Scott1974-1/TL-D3/Images/IMG_0604.JPG

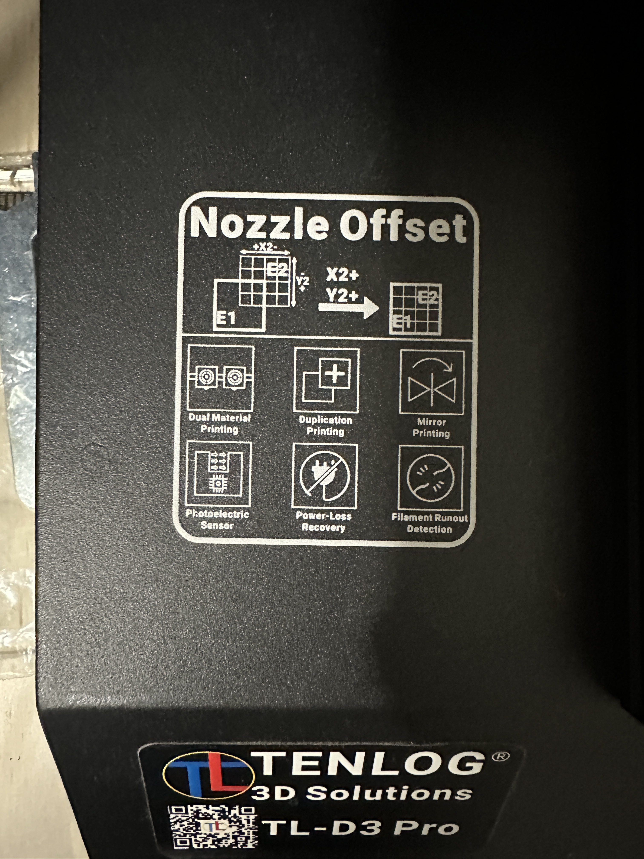
Images/IMG_0604.JPG
