Scott1974-1/TL-D3/Images/IMG_0610.JPG

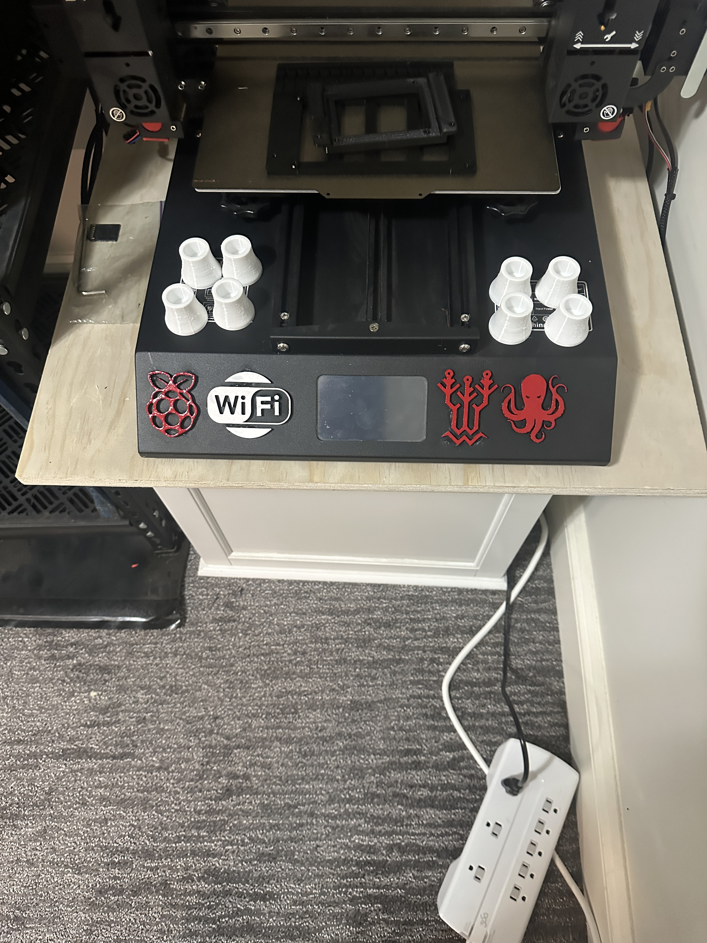
Images/IMG_0610.JPG
