Scott1974-1/TL-D3/Useful STL Files for the TL-D3 Pro /5015 Fanduct/images/cover_t1.png

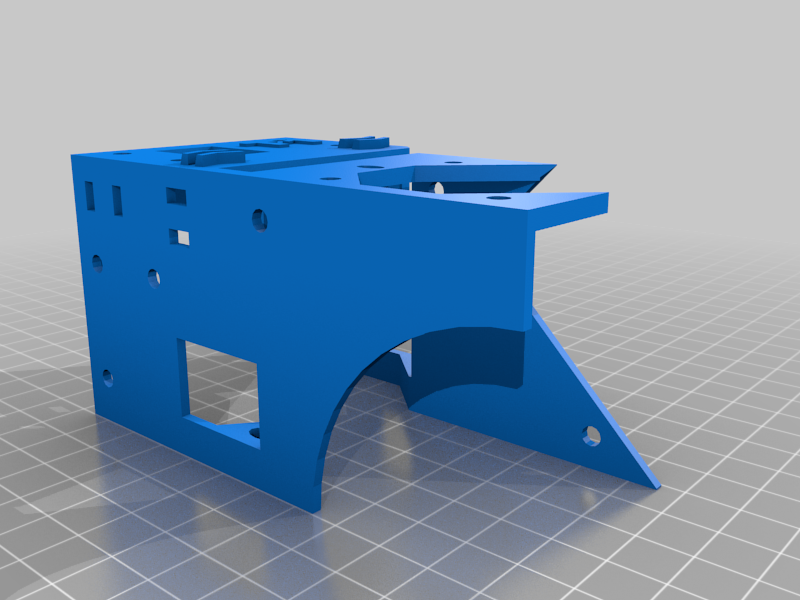
Useful STL Files for the TL-D3 Pro /5015 Fanduct/images/cover_t1.png
