Scott1974-1/TL-D3/Useful STL Files for the TL-D3 Pro /5015 Fanduct/images/DC_T1_fanduct_Text.png

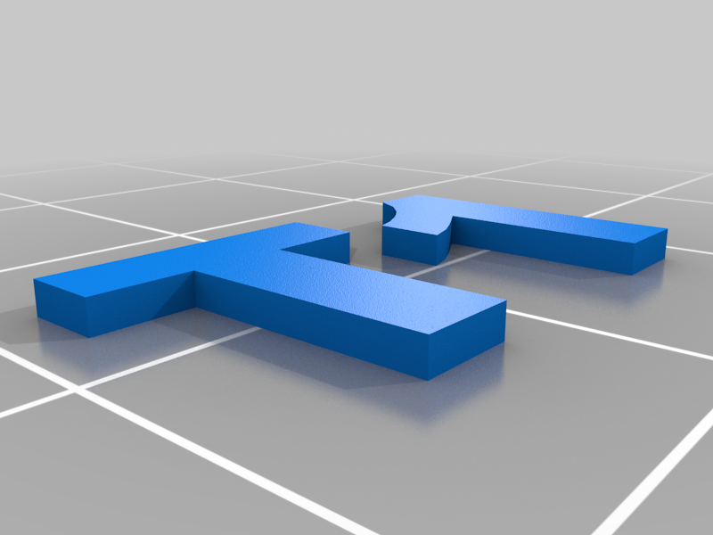
Useful STL Files for the TL-D3 Pro /5015 Fanduct/images/DC_T1_fanduct_Text.png
