Scott1974-1/TL-D3/Useful STL Files for the TL-D3 Pro /5015 Fanduct/images/foto_1.jpg

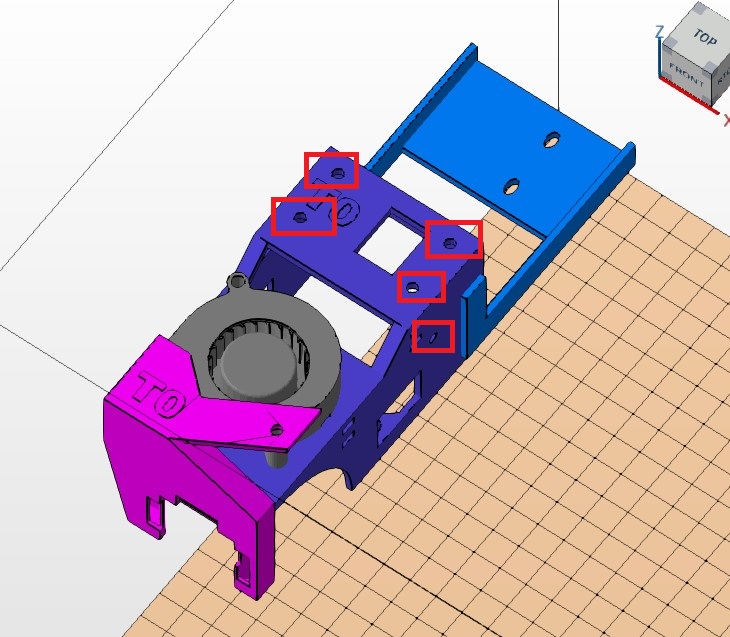
Useful STL Files for the TL-D3 Pro /5015 Fanduct/images/foto_1.jpg
