Scott1974-1/TL-D3/Useful STL Files for the TL-D3 Pro /Purge Bin w_ Modular Inserts/images/TLD3pro_Purge_Bin_3.jpg

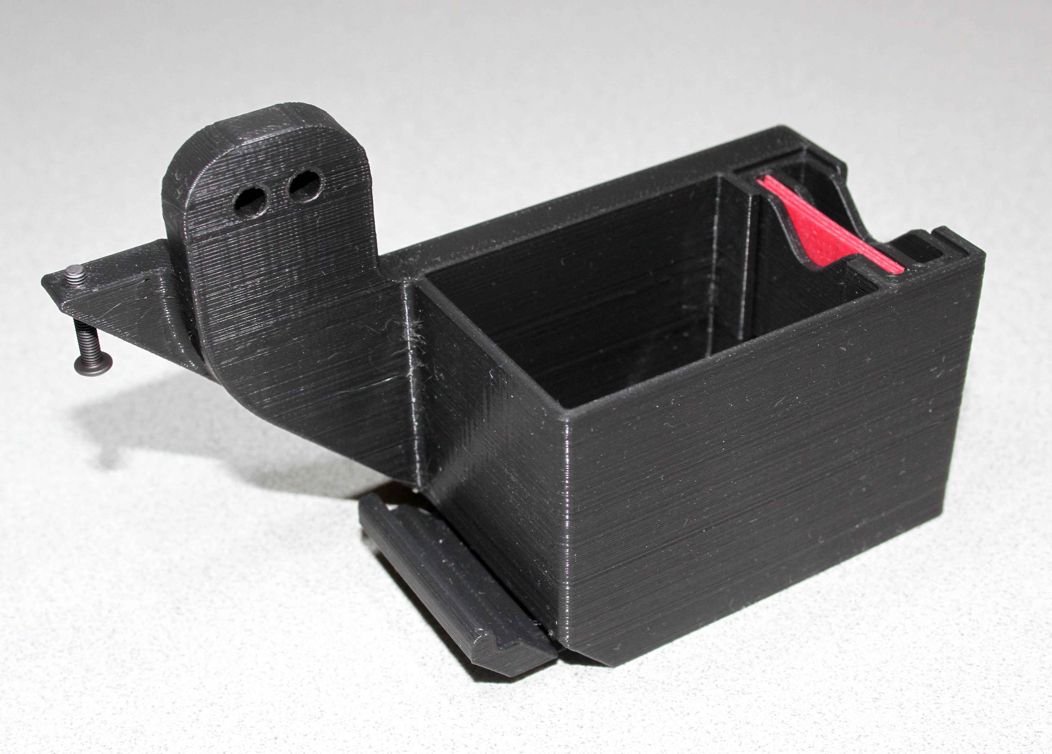
Useful STL Files for the TL-D3 Pro /Purge Bin w_ Modular Inserts/images/TLD3pro_Purge_Bin_3.jpg
