Scott1974-1/TL-D3/Useful STL Files for the TL-D3 Pro /Spool Holders/images/LH_Spool_Holder_Tenlog_TL-D3_Pro.png

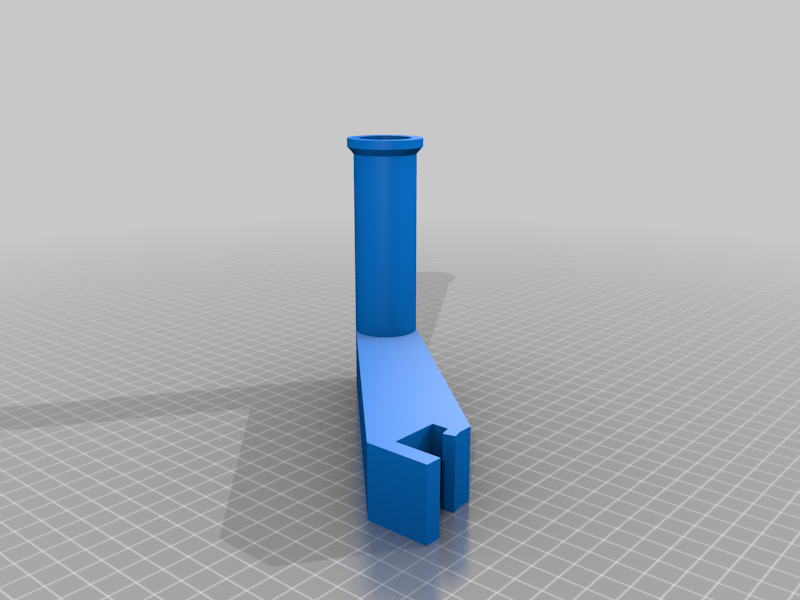
Useful STL Files for the TL-D3 Pro /Spool Holders/images/LH_Spool_Holder_Tenlog_TL-D3_Pro.png
