Scott1974-1/TL-D3/Useful STL Files for the TL-D3 Pro /Spool Holders/images/tenlog-spool-holder.jpg

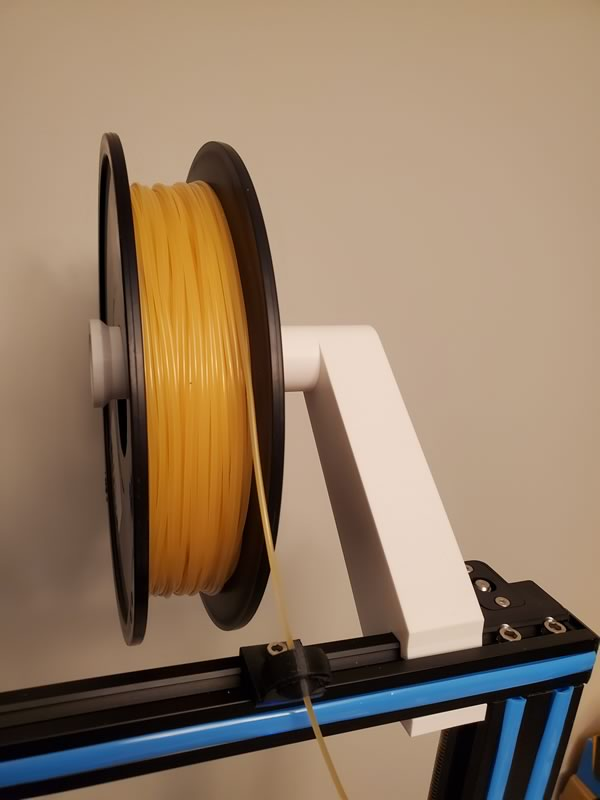
Useful STL Files for the TL-D3 Pro /Spool Holders/images/tenlog-spool-holder.jpg
