Scott1974-1/TL-D3/Useful STL Files for the TL-D3 Pro /Tenlog TL-D3 Pro TPU Foot/images/IMG_20220204_084932120.jpg

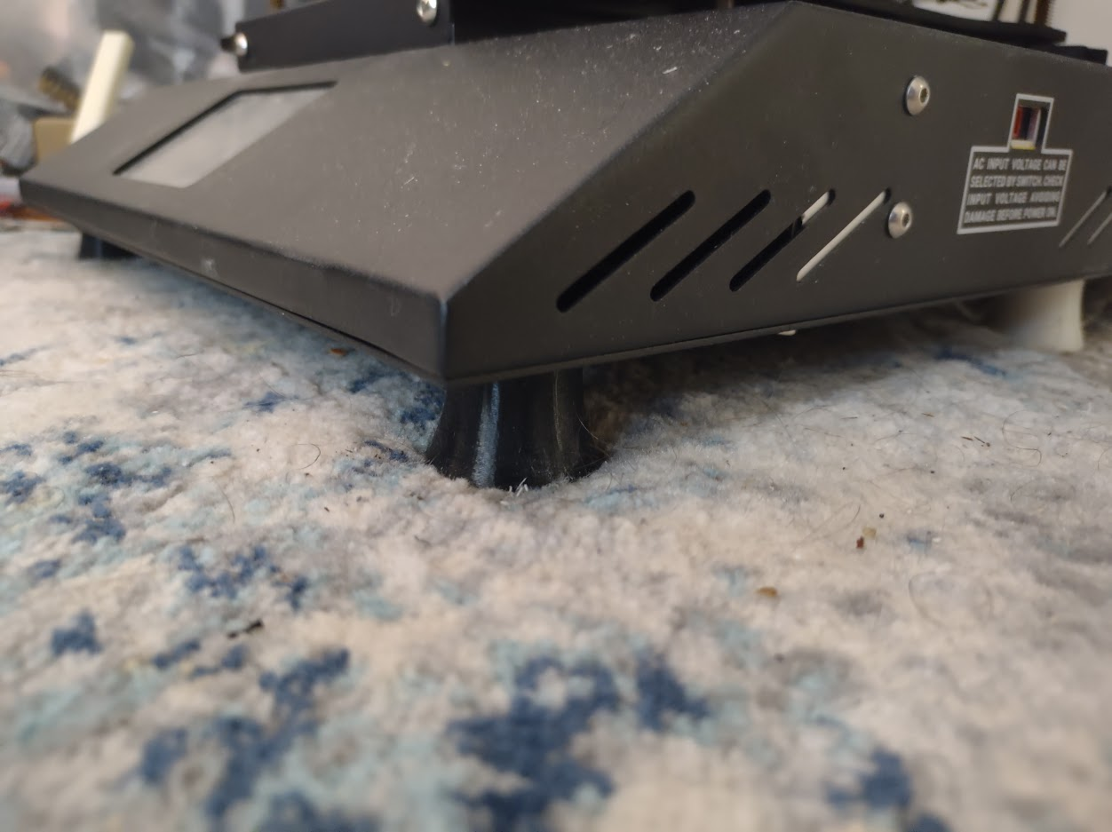
Useful STL Files for the TL-D3 Pro /Tenlog TL-D3 Pro TPU Foot/images/IMG_20220204_084932120.jpg
