Scott1974-1/TL-D3/TL-D3 Cura Profiles/meshes/TL-D4Pro.stl

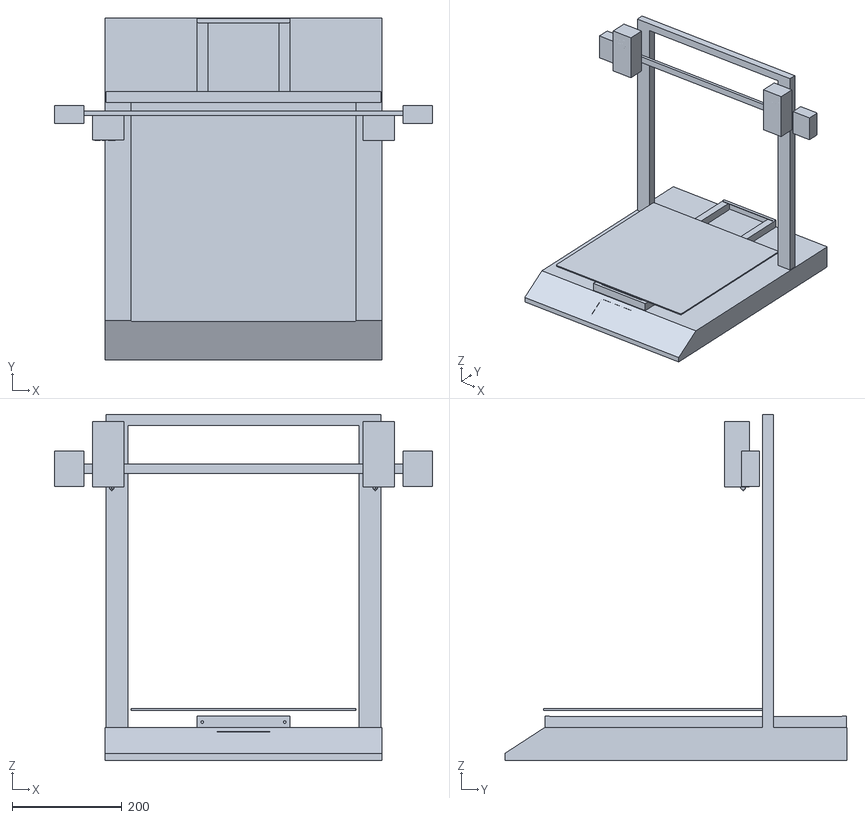
[picture p49: CAD file, 2025-01-07]
TL-D3 Cura Profiles/meshes/TL-D4Pro.stl
687.8 x 622.5 x 630.0
