Scott1974-1/TL-D3/Useful STL Files for the TL-D3 Pro /5015 Fanduct/files/DC_T0_fanduct_Text.stl

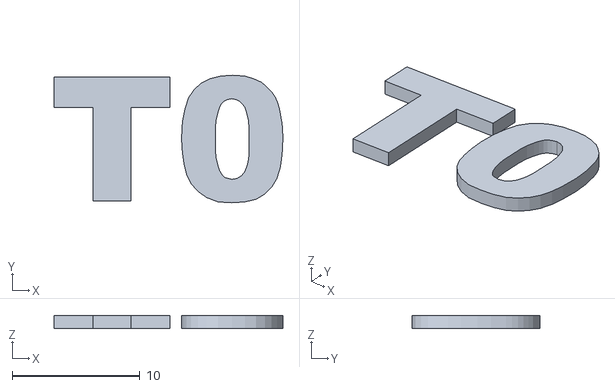
[picture p50: CAD file, 2025-01-07]
Useful STL Files for the TL-D3 Pro /5015 Fanduct/files/DC_T0_fanduct_Text.stl
18.0 x 10.0 x 1.00
