Scott1974-1/TL-D3/Useful STL Files for the TL-D3 Pro /BTT Super Case/SV03_Controller_RPI_Case.stl

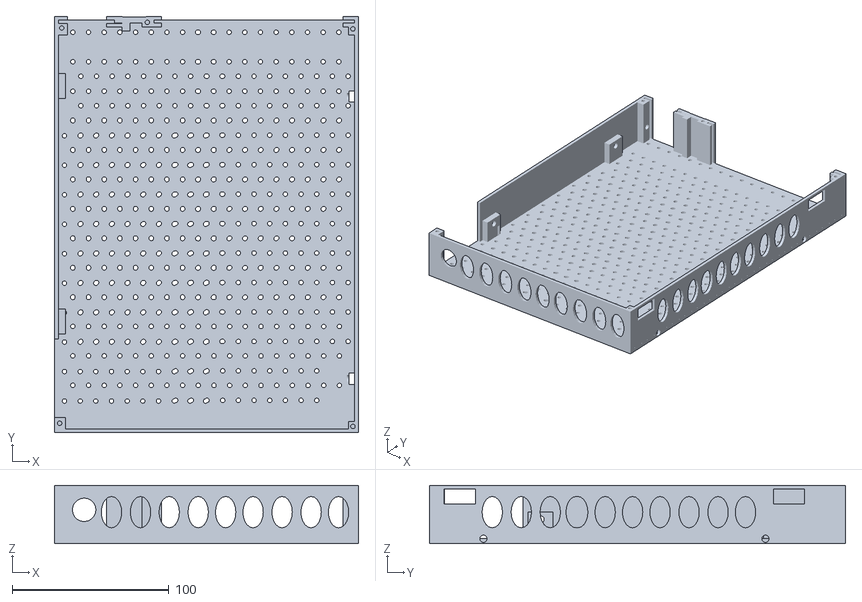
[picture p51: CAD file, 2025-01-07]
Useful STL Files for the TL-D3 Pro /BTT Super Case/SV03_Controller_RPI_Case.stl
193.9 x 265.6 x 37.0
