Scott1974-1/TL-D3/Useful STL Files for the TL-D3 Pro /Filament guide.stl

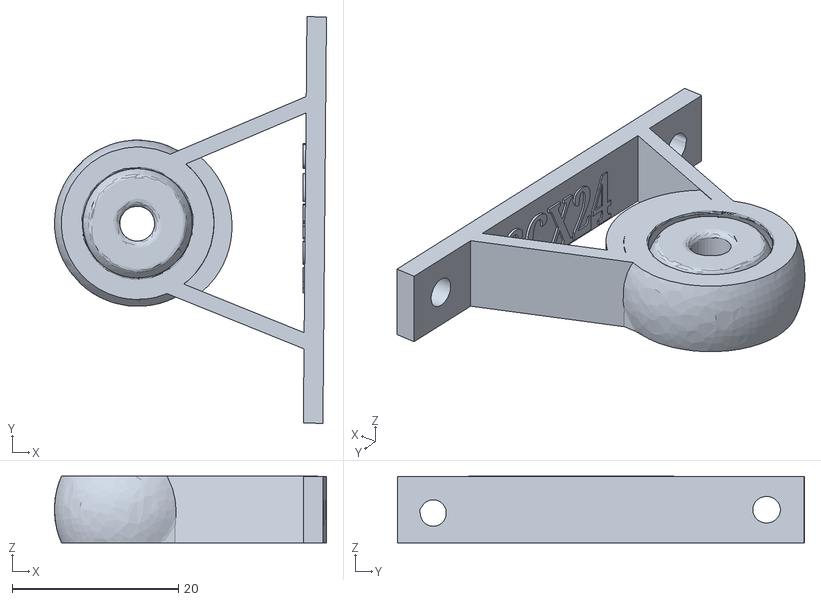
[picture p52: CAD file, 2025-01-09]
Useful STL Files for the TL-D3 Pro /Filament guide.stl
32.7 x 48.9 x 8.01
