Scott1974-1/TL-D3/Useful STL Files for the TL-D3 Pro /JST-XH Protectors /2pin/JST_Top2P-c2.stl

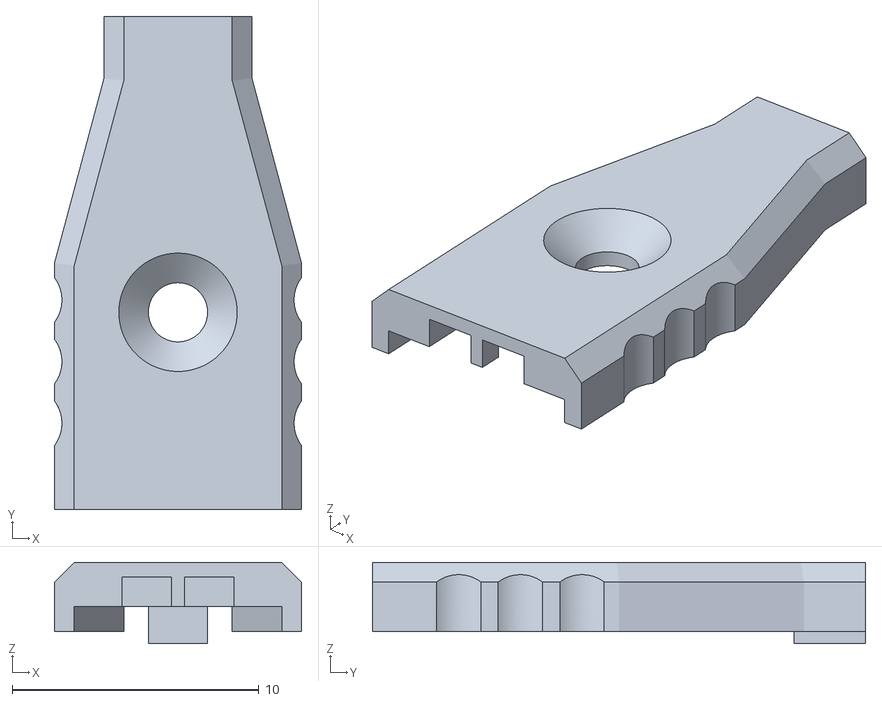
[picture p53: CAD file, 2025-01-08]
Useful STL Files for the TL-D3 Pro /JST-XH Protectors /2pin/JST_Top2P-c2.stl
10.0 x 20.0 x 3.30
