Scott1974-1/TL-D3/Useful STL Files for the TL-D3 Pro /JST-XH Protectors /3pin/JST_Top3P-c3.stl

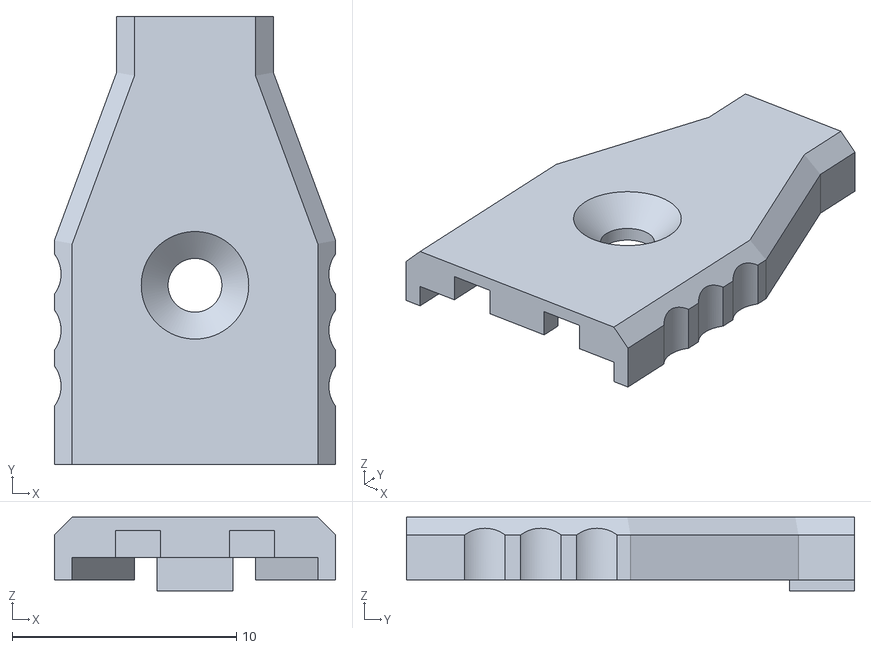
[picture p54: CAD file, 2025-01-08]
Useful STL Files for the TL-D3 Pro /JST-XH Protectors /3pin/JST_Top3P-c3.stl
12.6 x 20.0 x 3.30
