Scott1974-1/TL-D3/Useful STL Files for the TL-D3 Pro /JST-XH Protectors /4pin/JST_Top4P-c4.stl

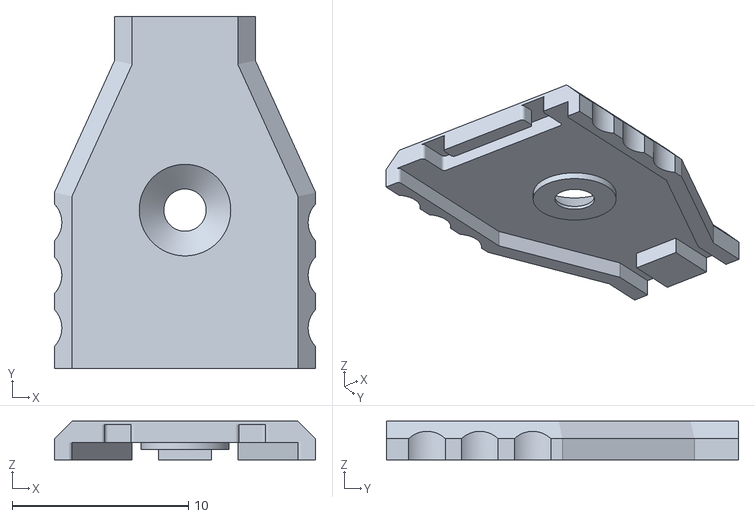
[picture p55: CAD file, 2025-01-08]
Useful STL Files for the TL-D3 Pro /JST-XH Protectors /4pin/JST_Top4P-c4.stl
14.8 x 20.0 x 2.20
