Scott1974-1/TL-D3/Useful STL Files for the TL-D3 Pro /Logos/BTT_Octopus_Logo_v3.stl

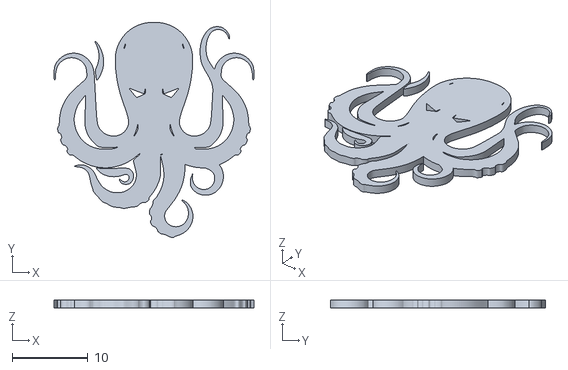
[picture p56: CAD file, 2025-01-07]
Useful STL Files for the TL-D3 Pro /Logos/BTT_Octopus_Logo_v3.stl
26.5 x 28.5 x 1.00
