Scott1974-1/TL-D3/Useful STL Files for the TL-D3 Pro /Purge Bin w_ Modular Inserts/files/TLD3pro_Purge_Bin.stl

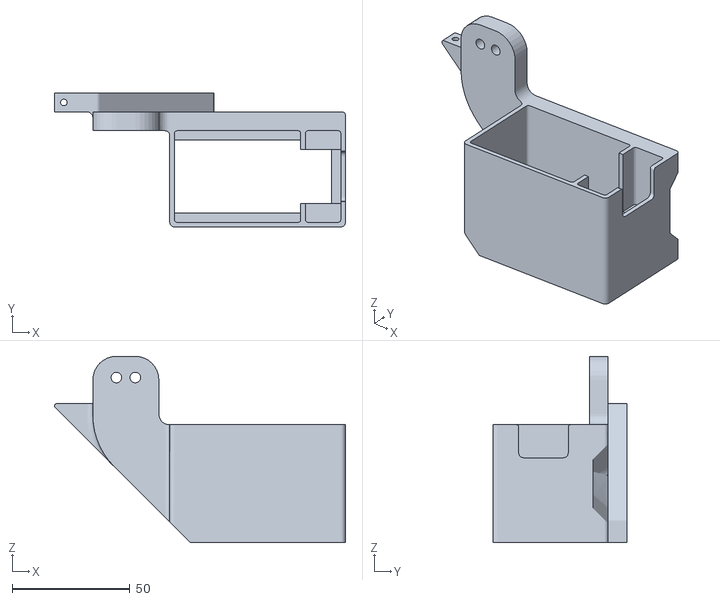
[picture p57: CAD file, 2025-01-07]
Useful STL Files for the TL-D3 Pro /Purge Bin w_ Modular Inserts/files/TLD3pro_Purge_Bin.stl
123.4 x 56.8 x 79.0
