Scott1974-1/TL-D3/Useful STL Files for the TL-D3 Pro /tenlog-tl-d3-pro-z-stabilizer/Z_bottom_right_D12_RV01.STL

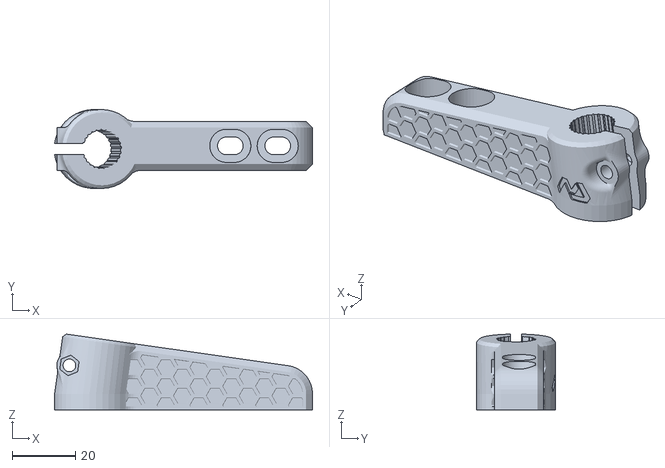
[picture p58: CAD file, 2025-01-07]
Useful STL Files for the TL-D3 Pro /tenlog-tl-d3-pro-z-stabilizer/Z_bottom_right_D12_RV01.STL
81.7 x 25.0 x 24.0
