Scott1974-1/TL-D3/Useful STL Files for the TL-D3 Pro /Testing/Bed level and nozzle offset/files/TLD_BL2.stl

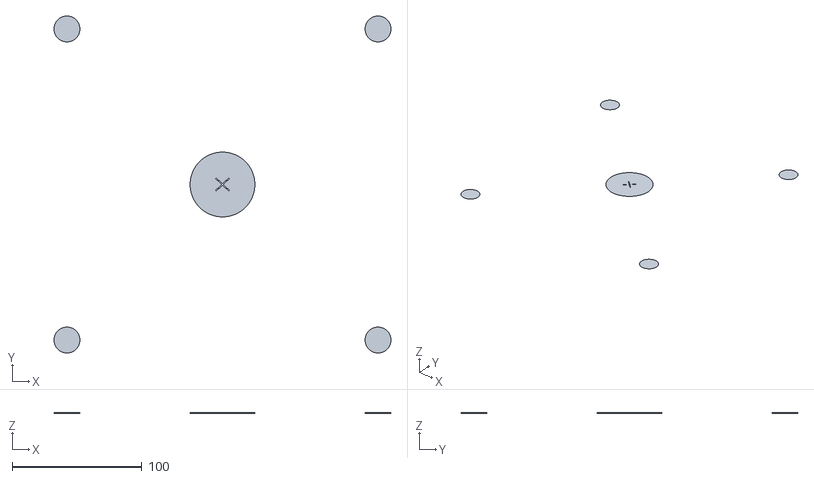
[picture p59: CAD file, 2025-01-07]
Useful STL Files for the TL-D3 Pro /Testing/Bed level and nozzle offset/files/TLD_BL2.stl
260.0 x 260.0 x 0.2
