Scott1974-1/TL-D3/TL-D3 Cura Profiles/meshes/TL-D3Pro.stl

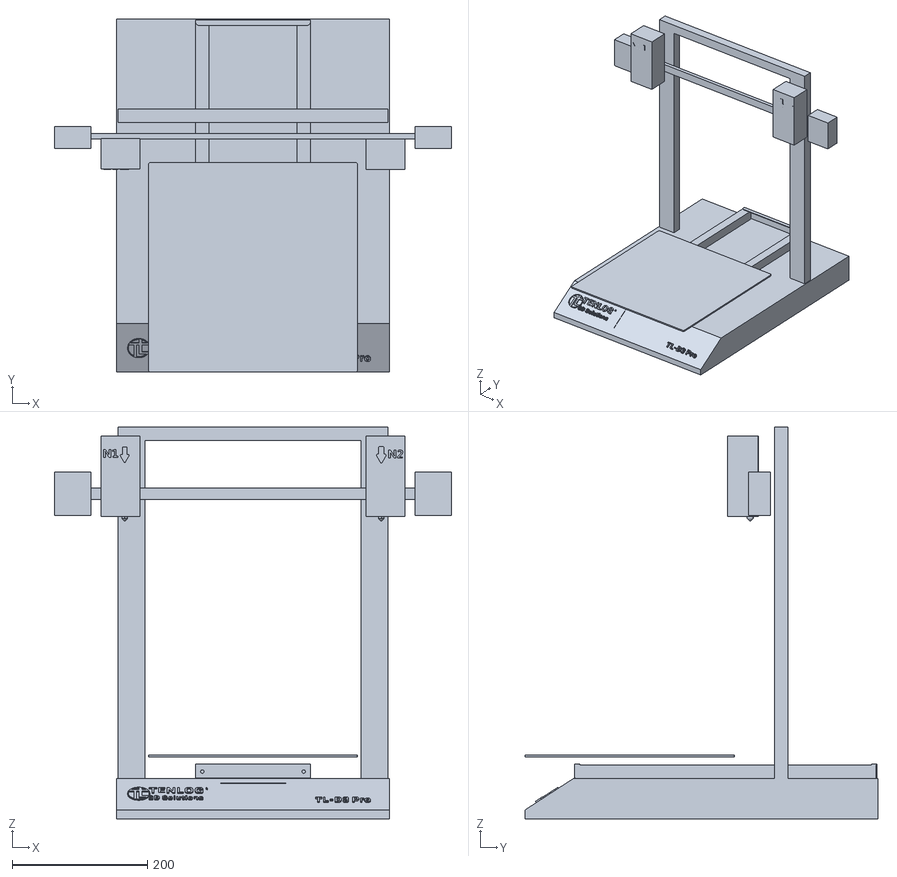
[picture p60: CAD file, 2025-01-07]
TL-D3 Cura Profiles/meshes/TL-D3Pro.stl
587.8 x 522.6 x 580.0
