Scott1974-1/TL-D3/Useful STL Files for the TL-D3 Pro /5015 Fanduct/files/DC_T1_cover_Text.stl

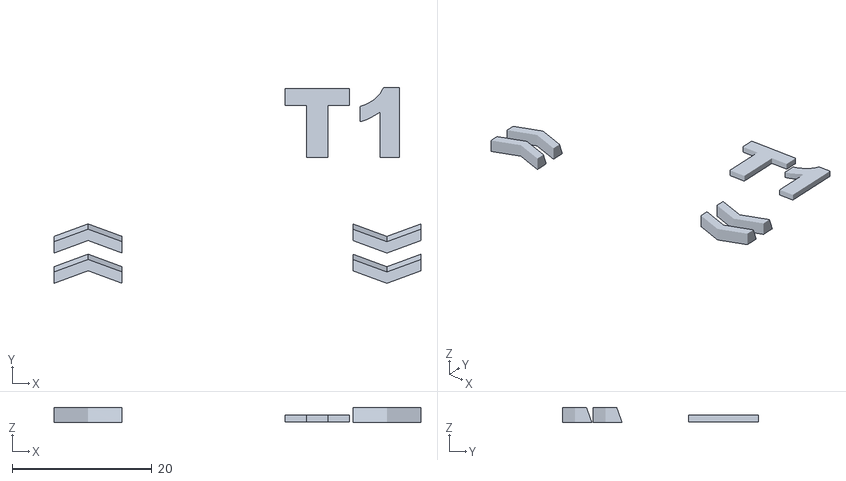
[picture p61: CAD file, 2025-01-07]
Useful STL Files for the TL-D3 Pro /5015 Fanduct/files/DC_T1_cover_Text.stl
52.5 x 28.0 x 2.10
