Scott1974-1/TL-D3/Useful STL Files for the TL-D3 Pro /Cable guide.stl

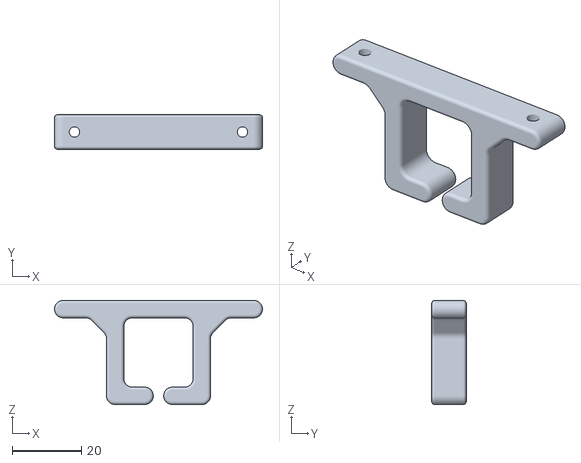
[picture p62: CAD file, 2025-01-09]
Useful STL Files for the TL-D3 Pro /Cable guide.stl
60.0 x 10.0 x 30.0
