Scott1974-1/TL-D3/Useful STL Files for the TL-D3 Pro /Purge Bin w_ Modular Inserts/files/TLD3pro_Purge_Bin_Brush_Insert.stl

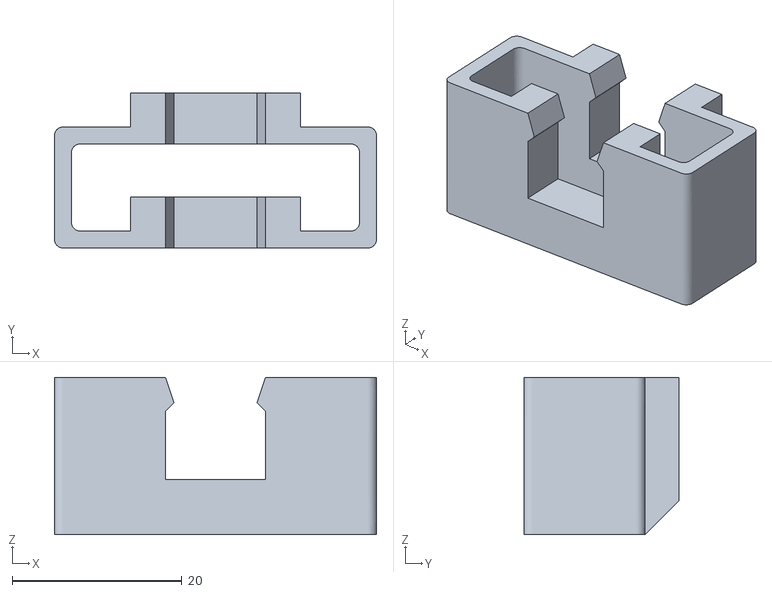
[picture p63: CAD file, 2025-01-07]
Useful STL Files for the TL-D3 Pro /Purge Bin w_ Modular Inserts/files/TLD3pro_Purge_Bin_Brush_Insert.stl
37.9 x 18.2 x 18.5
