Scott1974-1/TL-D3/TL-D3 Cura Profiles/meshes/TL-D5Pro.stl

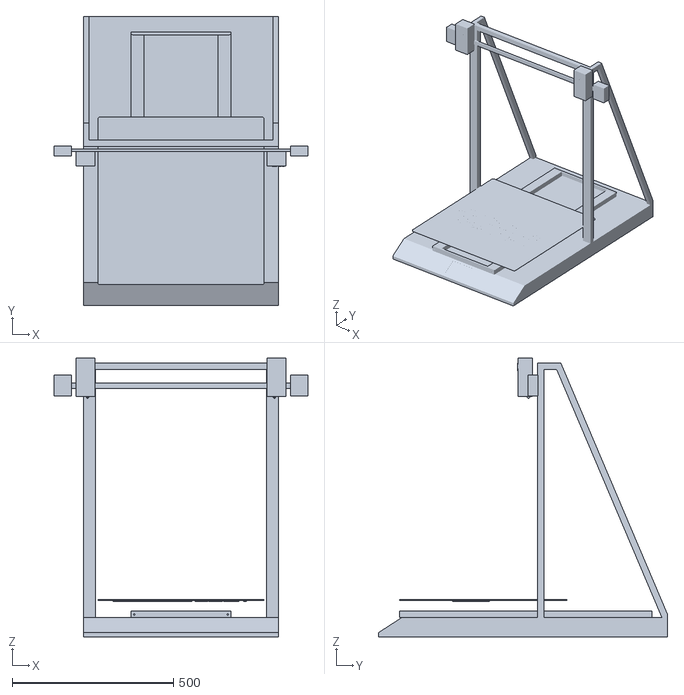
[picture p64: CAD file, 2025-01-07]
TL-D3 Cura Profiles/meshes/TL-D5Pro.stl
787.8 x 897.5 x 865.8
