Scott1974-1/TL-D3/Useful STL Files for the TL-D3 Pro /19_mm_wrench.stl

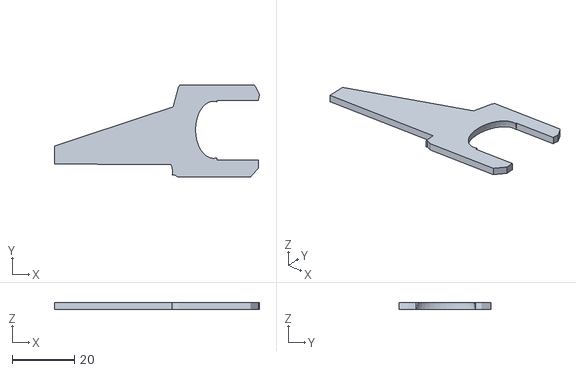
[picture p65: CAD file, 2025-01-08]
Useful STL Files for the TL-D3 Pro /19_mm_wrench.stl
65.9 x 29.7 x 2.11
