Scott1974-1/TL-D3/Useful STL Files for the TL-D3 Pro /5015 Fanduct/files/T0_cover.stl

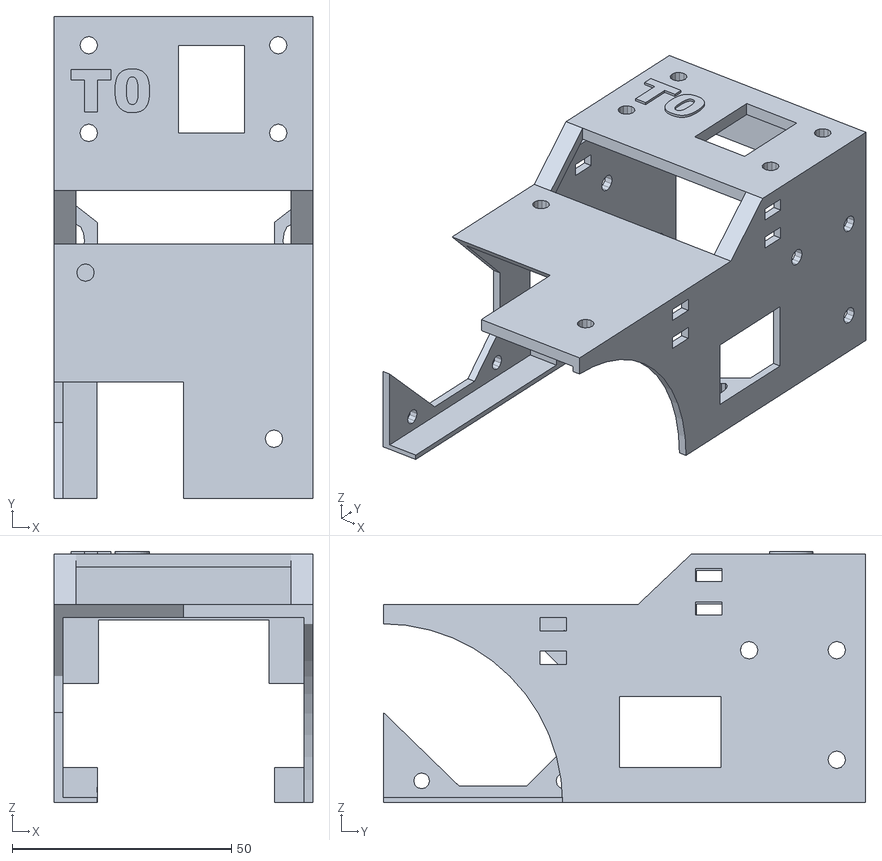
[picture p66: CAD file, 2025-01-07]
Useful STL Files for the TL-D3 Pro /5015 Fanduct/files/T0_cover.stl
59.0 x 110.0 x 57.4
