Scott1974-1/TL-D3/Useful STL Files for the TL-D3 Pro /Purge Bin w_ Modular Inserts/files/TLD3pro_Purge_Bin_Insert_Blank.stp

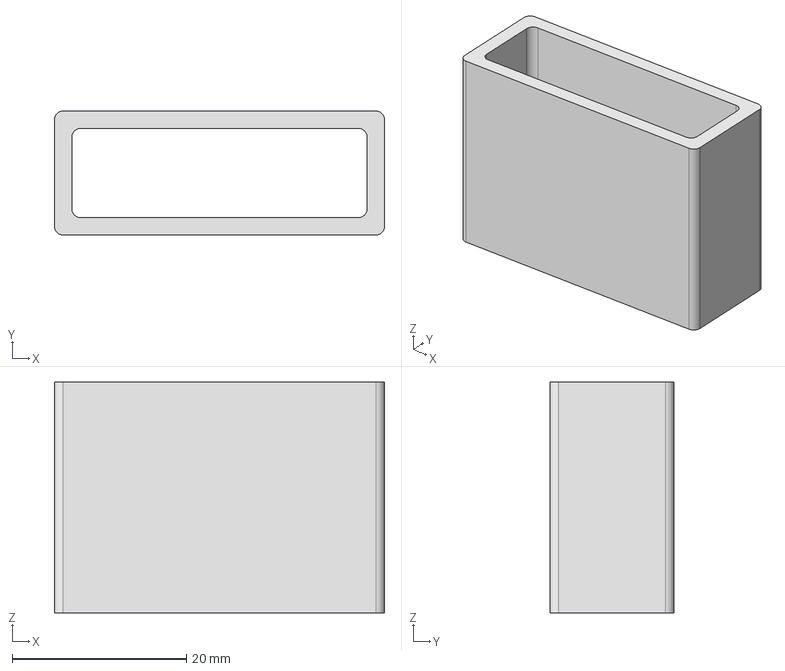
[picture p67: CAD file, 2025-01-07]
Useful STL Files for the TL-D3 Pro /Purge Bin w_ Modular Inserts/files/TLD3pro_Purge_Bin_Insert_Blank.stp
37.9 x 14.3 x 26.5 mm
