Scott1974-1/TL-D3/Useful STL Files for the TL-D3 Pro /E2_Tool_Holder.stl

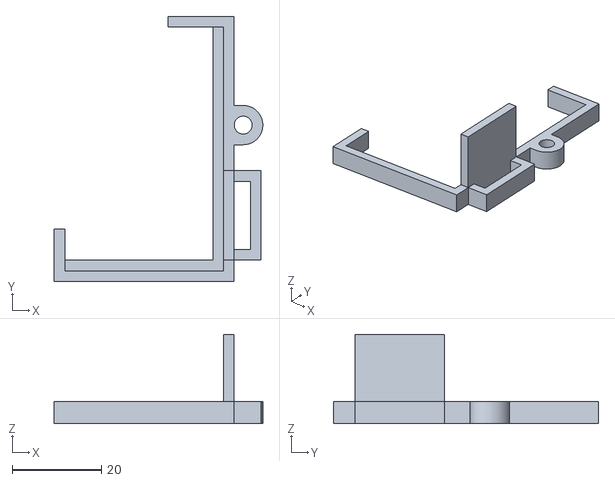
[picture p70: CAD file, 2025-01-07]
Useful STL Files for the TL-D3 Pro /E2_Tool_Holder.stl
46.7 x 59.3 x 20.0
