Scott1974-1/TL-D3/Useful STL Files for the TL-D3 Pro /Purge Bin w_ Modular Inserts/files/TLD3pro_Purge_Bin_Bottom.stl

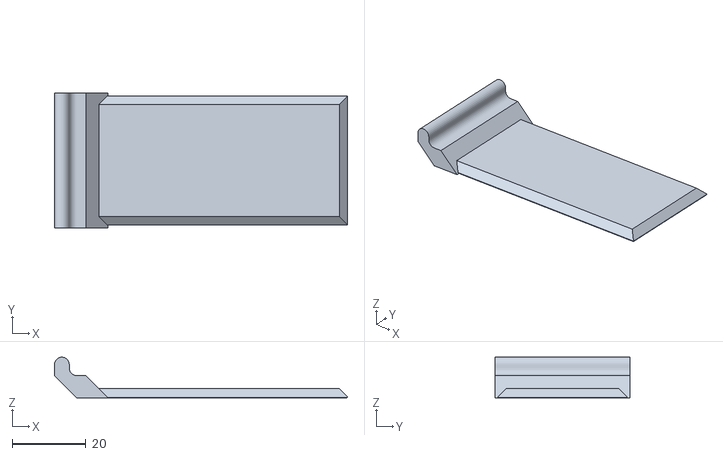
[picture p71: CAD file, 2025-01-07]
Useful STL Files for the TL-D3 Pro /Purge Bin w_ Modular Inserts/files/TLD3pro_Purge_Bin_Bottom.stl
79.2 x 36.4 x 11.0
