Scott1974-1/TL-D3/Useful STL Files for the TL-D3 Pro /BTT_Octopus_Mount.stl

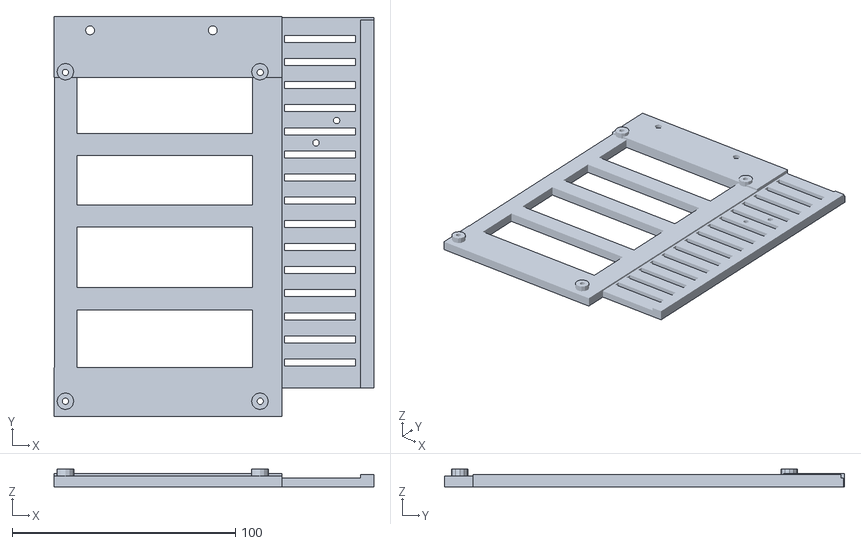
[picture p73: CAD file, 2025-01-07]
Useful STL Files for the TL-D3 Pro /BTT_Octopus_Mount.stl
143.0 x 179.0 x 8.00
