Scott1974-1/TL-D3/Useful STL Files for the TL-D3 Pro /5015 Fanduct/files/fanduct_t1.stl

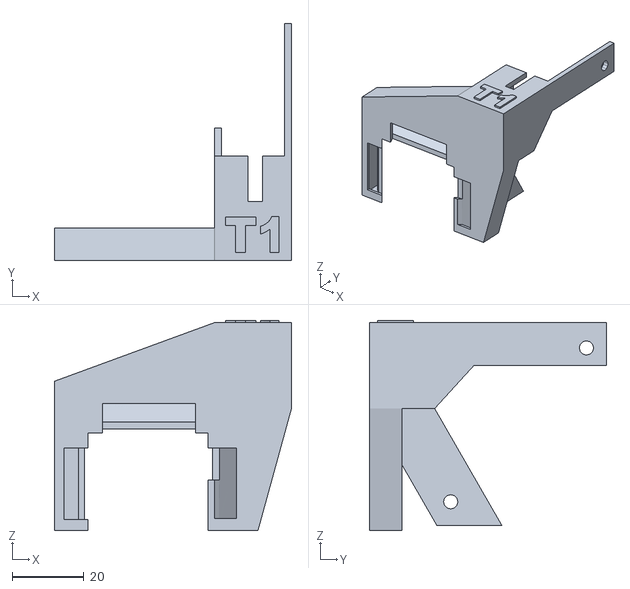
[picture p74: CAD file, 2025-01-07]
Useful STL Files for the TL-D3 Pro /5015 Fanduct/files/fanduct_t1.stl
66.2 x 66.2 x 58.7
