Scott1974-1/TL-D3/Useful STL Files for the TL-D3 Pro /TFT35_mount.STL

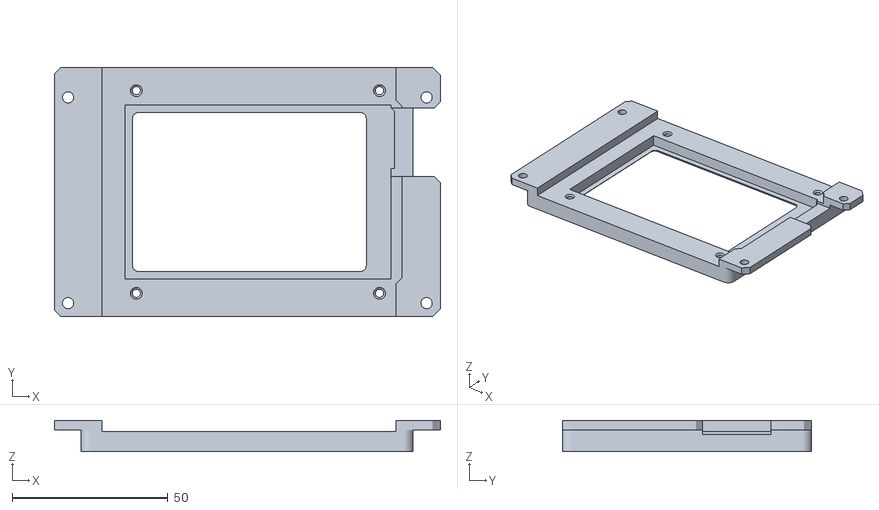
[picture p75: CAD file, 2025-01-07]
Useful STL Files for the TL-D3 Pro /TFT35_mount.STL
123.8 x 80.0 x 10.00
