Scott1974-1/TL-D3/Useful STL Files for the TL-D3 Pro /5015 Fanduct/files/T0_RunOut.stl

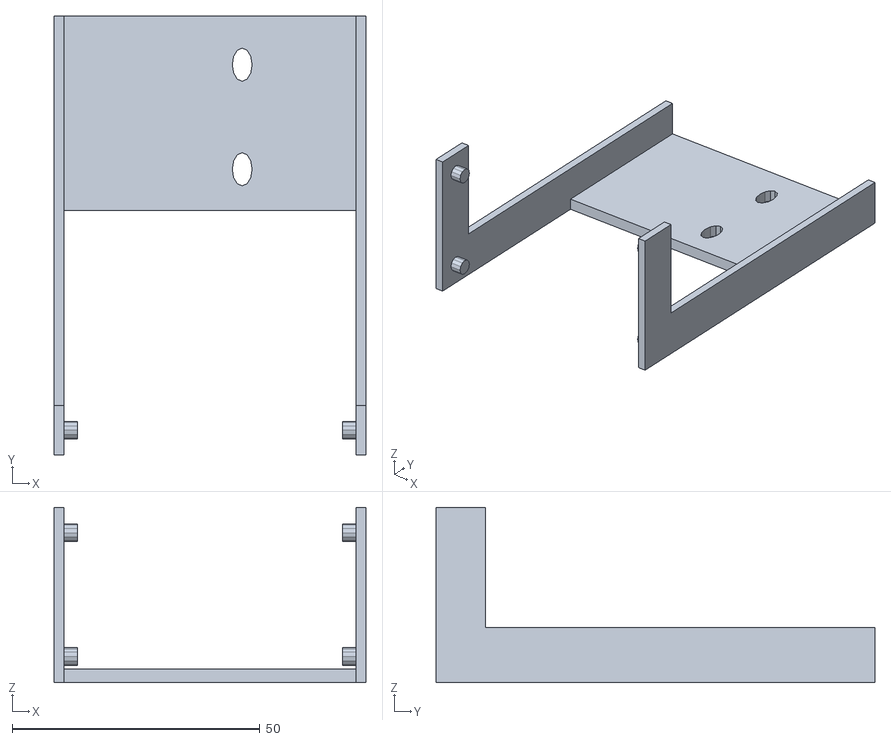
[picture p76: CAD file, 2025-01-07]
Useful STL Files for the TL-D3 Pro /5015 Fanduct/files/T0_RunOut.stl
63.0 x 88.7 x 35.4
