Scott1974-1/TL-D3/Useful STL Files for the TL-D3 Pro /5015 Fanduct/files/DC_T0_fanduct.stl

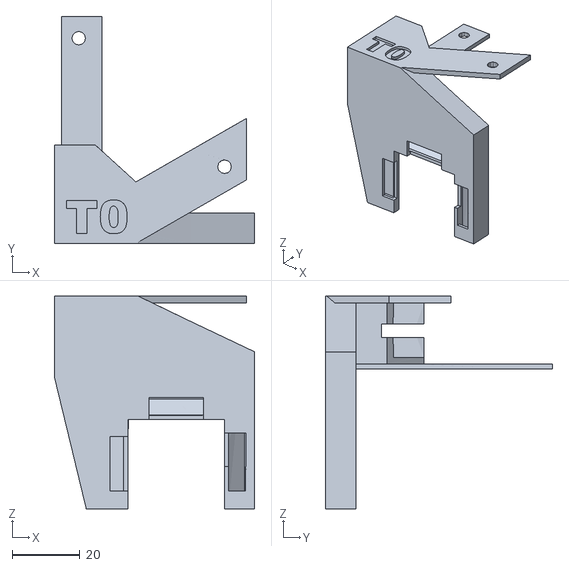
[picture p77: CAD file, 2025-01-07]
Useful STL Files for the TL-D3 Pro /5015 Fanduct/files/DC_T0_fanduct.stl
59.0 x 67.0 x 62.7
