Scott1974-1/TL-D3/Useful STL Files for the TL-D3 Pro /5015 Fanduct/files/cover_t1.stl

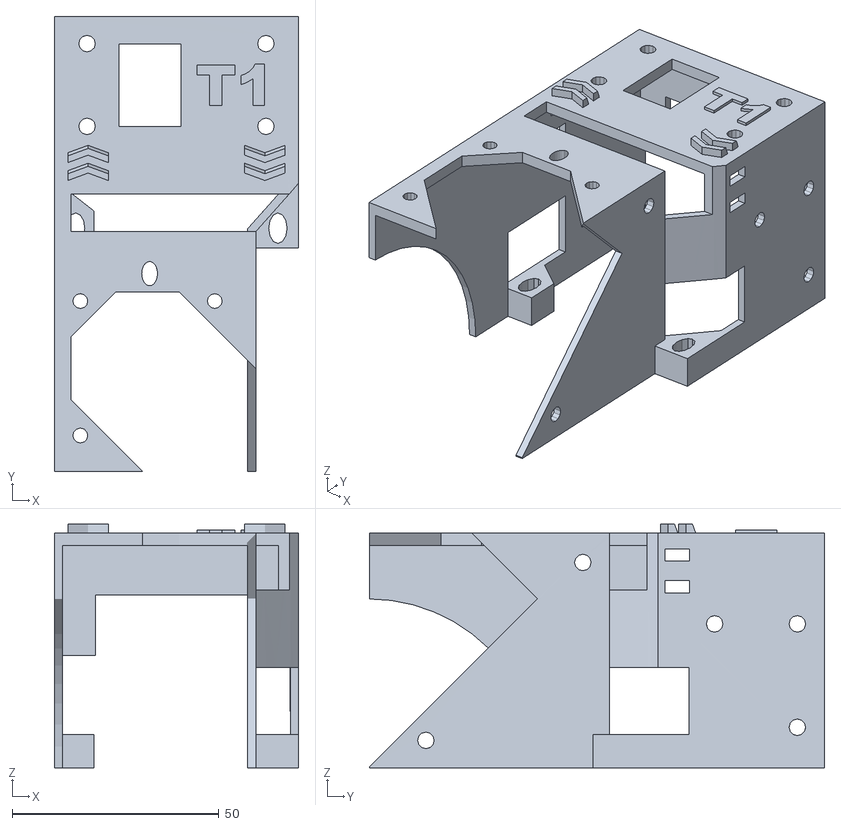
[picture p78: CAD file, 2025-01-07]
Useful STL Files for the TL-D3 Pro /5015 Fanduct/files/cover_t1.stl
59.0 x 110.0 x 58.9
