Scott1974-1/TL-D3/Useful STL Files for the TL-D3 Pro /5015 Fanduct/files/T0_Fanduct_.stl

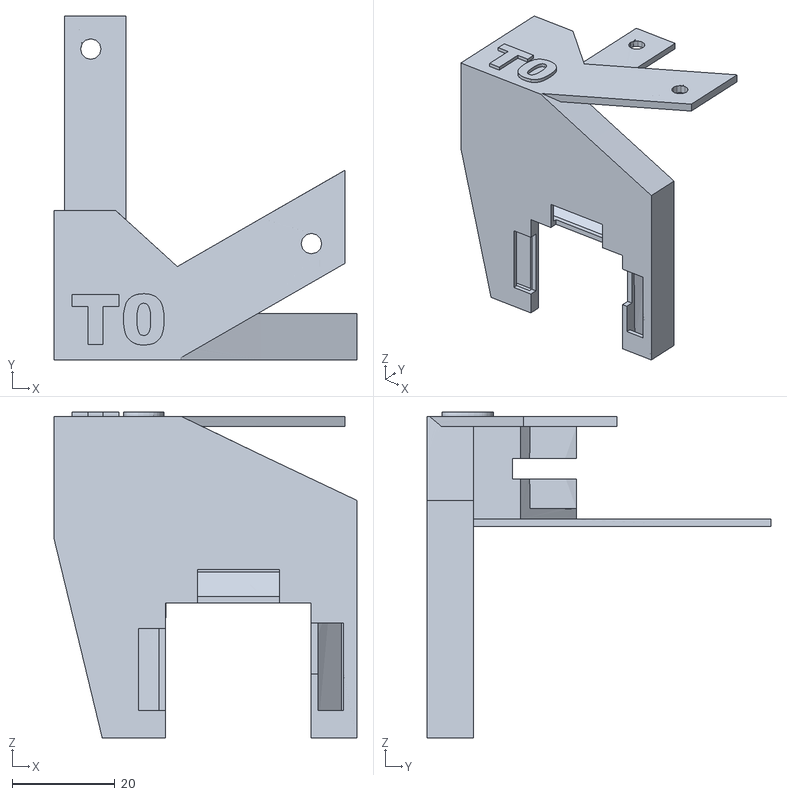
[picture p79: CAD file, 2025-01-07]
Useful STL Files for the TL-D3 Pro /5015 Fanduct/files/T0_Fanduct_.stl
59.0 x 67.0 x 63.6
