Scott1974-1/TL-D3/Useful STL Files for the TL-D3 Pro /Testing/Bed level and nozzle offset/images/TLD_BL2.png

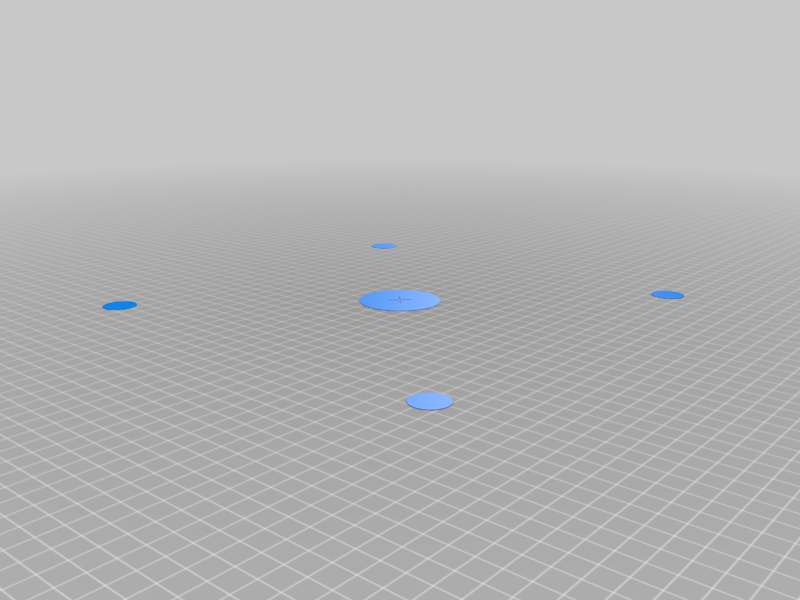
Useful STL Files for the TL-D3 Pro /Testing/Bed level and nozzle offset/images/TLD_BL2.png
