Scott1974-1/TL-D3/Images/IMG_0603.JPG

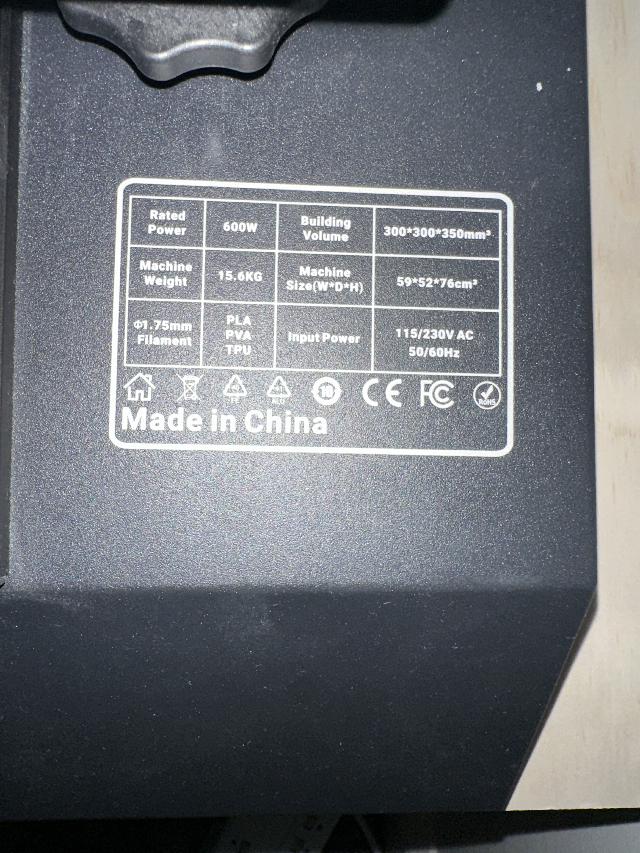
Images/IMG_0603.JPG
